ketaro/ESP8266_DHT22_TempSensor/Config.cpp

//
// config.cpp - Library for handling storing and retrieving 
//              config settings from EEPROM
//

#include <EEPROM.h>

#include "Arduino.h"
#include "Config.h"
#include "defaults.h"
#include "math.h"

Config::Config() {
  // init EEPROM, all 512 bytes
  EEPROM.begin( EEPROM_SIZE );

  readConfig();
}


void Config::readConfig() {
  unsigned int current_version;

  Serial.print( "READING CONFIG FROM EEPROM.  VERSION: " );

  // Read the config version number from eeprom
  EEPROM.get( EEPROM_CONFIG_START, current_version );
  Serial.println( current_version, DEC );

  // If config version is not something we can upgrade from,
  // set a default config.
  if ( current_version != CONFIG_VERSION ) {
    Serial.println( "Unsupported or no config found in EEPROM.  Resettings to defaults." );
    conf = _defaults;
    writeConfig();
  }

  // Read EEPROMP into config struct
  EEPROM.get( EEPROM_CONFIG_START, conf );
}


//
// Update a value in the running config (does not commit)
// Truncates strings that exceed the max length for any field.
bool Config::set( int key, String value ) {
  Serial.println( "Config::set( " + String(key) + ", " + value + ")" );

  switch( key ) {
    case CONFIG_HOSTNAME:
      strcpy( conf.hostname, value.substring(0, MAX_HOSTNAME).c_str() );
      break;
    case CONFIG_SSID:
      strcpy( conf.ssid, value.substring(0, MAX_SSID).c_str() );
      break;
    case CONFIG_WIFI_PW:
      strcpy( conf.wifi_pw, value.substring(0, MAX_WIFI_PW).c_str() );
      break;

    case CONFIG_DB_TYPE:
      // Convert string to int.  Valid range 0 - 2
      unsigned short dbtype;
      dbtype = value.toInt();

      if ( dbtype >= 0 && dbtype < 3 )
        conf.db_type = dbtype;
      else
        return false;

      break;
    
    case CONFIG_DB_HOST:
      strcpy( conf.db_host, value.substring(0, MAX_DB_HOST).c_str() );
      break;

    case CONFIG_DB_PORT:
      // Convert string to int.  Valid port range 1 - 65535
      long port;
      port = value.toInt();

      if ( port > 0 && port < 65535 )
        conf.db_port = port;
      else
        return false;

      break;

    case CONFIG_DB_NAME:
      strcpy( conf.db_name, value.substring(0, MAX_DB_NAME).c_str() );
      break;

    case CONFIG_SAMPLE_INTERVAL:
      // Convert string to int.  Valid range 1 - 86400
      long interval;
      interval = value.toInt();

      if ( interval > 0 && interval <= 86400 )
        conf.sample_interval = interval;
      else
        return false;

      break;

    case CONFIG_DB_MEASUREMENT:
      strcpy( conf.db_measurement, value.substring(0, MAX_DB_MEASUREMENT).c_str() );
      break;

    case CONFIG_LOCATION:
      strcpy( conf.location, value.substring(0, MAX_LOCATION).c_str() );
      break;

    case CONFIG_HTTP_PW:
      strcpy( conf.http_pw, value.substring(0, MAX_HTTP_PW).c_str() );
      break;

    case CONFIG_T_OFFSET:
      conf.t_offset = atof(value.c_str());
      break;

    default:
      Serial.println( "[Config::set] Unknown config key: " + String(key) + " = " + value );
      return false;
  }

  return true;

}


// Save the running config
void Config::writeConfig() {
  Serial.print( "Clearing EEPROM, size: " );
  Serial.println( EEPROM.length() );
  for (int i = 0 ; i < EEPROM.length() ; i++) {
    EEPROM.write(i, 0);
  }
  EEPROM.commit();
  
  Serial.println( "Writing config to EEPROM" );
  EEPROM.put( EEPROM_CONFIG_START, conf );
  EEPROM.commit();
}


// Reset the running config
void Config::resetConfig() {
  conf = _defaults;
  writeConfig();
}


// Returns a JSON String of the current config
String Config::JSON(String macaddr) {
  bool wifiPassSaved = false;

  if (String(conf.wifi_pw).length() > 0)
    wifiPassSaved = true;
  
  String jsonstr = "{\"ver\": \"" + String(conf.version) + "\", " 
                   "\"ino_ver\": \"" + INO_VERSION + "\", "
                   "\"mac\": \"" + macaddr + "\", "
                   "\"hostname\": \"" + String(conf.hostname) + "\", "
                   "\"db\": {"
                       "\"db_name\": \"" + String(conf.db_name) + "\", "
                       "\"db_host\": \"" + String(conf.db_host) + "\", "
                       "\"location\": \"" + String(conf.location) + "\", "
                       "\"db_measurement\": \"" + String(conf.db_measurement) + "\", "
                       "\"db_type\": \"" + String(conf.db_type) + "\", "
                       "\"db_port\": \"" + String(conf.db_port) + "\", "
                       "\"interval\": \"" + String(conf.sample_interval) + "\", "
                       "\"t_offset\": \"" + String(conf.t_offset) + "\""
                       "}, "
                   "\"net\": {"
                       "\"ssid\": \"" + String(conf.ssid) + "\", "
                       "\"pw\": \"" + String(wifiPassSaved) + "\""
                       "}"
                   "}";

  return jsonstr;
}
